brainsmoke/usb2_hub/case/case_v0.1_bottom.scad

// case for the PCBs marked v0.1

use <case_v0.1.scad>

case();
