brainsmoke/usb2_hub/case/lightpipe_test.scad

use <case.scad>

intersection()
{
flip()
top();
translate([-5,20,0]) cube([10,40,100]);
}
